jkmunson/RTOS_POD/PLAYER_FIRMWARE/Core/Inc/wav_header.h

unsigned char wav_header_bin[] = {
  0x52, 0x49, 0x46, 0x46, 0x24, 0xf8, 0x2b, 0x03, 0x57, 0x41, 0x56, 0x45,
  0x66, 0x6d, 0x74, 0x20, 0x10, 0x00, 0x00, 0x00, 0x01, 0x00, 0x01, 0x00,
  0x44, 0xac, 0x00, 0x00, 0x10, 0xb1, 0x02, 0x00, 0x04, 0x00, 0x10, 0x00,
  0x64, 0x61, 0x74, 0x61, 0x50, 0x75, 0x0d, 0x00
};
unsigned int wav_header_bin_len = 44;
