jkmunson/RTOS_POD/PLAYER_FIRMWARE/Core/Src/jeremy.c

#include "FreeRTOS.h"
#include "task.h"
#include "cmsis_os.h"
#include "stm32g4xx_hal.h"
#include "stm32g4xx_hal_dac.h"
#include "stm32g4xx_hal_dma.h"
#include "stm32g4xx_hal_tim.h"
#include "main.h"
#include "console.h"
#include "buttons.h"


#include <string.h>
#include <stdio.h>

extern DMA_HandleTypeDef hdma_dac1_ch1;
#define AUD_GREEN_L_DMA hdma_dac1_ch1;

extern UART_HandleTypeDef huart5;
//DAC_DHR12LD

size_t audio_dma_current_index;

void update_green_DMA_addr(void){
	audio_dma_current_index = (audio_dma_current_index+4)%AUD_BUFFER_SIZE;
	const char *tim_msg = "DMA Update started or wrapped\n";
	HAL_UART_Transmit(&huart5,tim_msg,strlen(tim_msg), 0xFFFF);
	if ((audio_dma_current_index==0))	HAL_UART_Transmit(&huart5,tim_msg,strlen(tim_msg), 0xFFFF);
}

size_t get_audio_buffer_current_index(void){
	return audio_dma_current_index;
}


void jeremy_main(void *ignore __attribute__ ((unused))) {
	while(1){
		vTaskDelay(100);
		//console_print_blocked("Hi\n", 200);
	}
	/*
	const char *jeremy_main_msg = "Jeremy: Entered Jeremy Main\n";
	const char *jeremy_main_cb = "Jeremy: Registered timer callback\n";
	const char *jeremy_main_dma = "Jeremy: Initiated DMA\n";
	const char *jeremy_main_tim = "Jeremy: Initiated Timer\n";
	char buf[75];

	HAL_UART_Transmit(&huart5,jeremy_main_msg,strlen(jeremy_main_msg), 0xFFFF);

	HAL_TIM_Base_Start(&AUDIO_44_1_KHZ_TIMER);
	HAL_UART_Transmit(&huart5,jeremy_main_tim,strlen(jeremy_main_tim), 0xFFFF);
	HAL_DAC_Start(&AUD_GREEN_DAC, DAC_CHANNEL_1);
	HAL_DAC_Start(&AUD_GREEN_DAC, DAC_CHANNEL_2);

	HAL_DAC_Start_DMA(&AUD_GREEN_DAC, DAC_CHANNEL_1, (uint32_t*)audio_buffer, (AUD_BUFFER_SIZE>>2)-1 , DAC_ALIGN_12B_L);
	HAL_DAC_Start_DMA(&AUD_GREEN_DAC, DAC_CHANNEL_2, (uint32_t*)(audio_buffer+2), (AUD_BUFFER_SIZE>>2)-1 , DAC_ALIGN_12B_L);



	HAL_UART_Transmit(&huart5,jeremy_main_dma,strlen(jeremy_main_dma), 0xFFFF);
	audio_dma_current_index = 0; //Reset the index now, in case it had counted up before we started DMA. its okay to be a ways behind the dma.
	for(int i=0; 1; i++){
		sprintf(buf, "Jeremy: Uptime: %d\n", i, audio_dma_current_index);
		HAL_UART_Transmit(&huart5, buf, strlen(buf), 0xFFFF);
		vTaskDelay(1000);
	}*/
	vTaskSuspend(NULL); //LEAVE AT THE END
	vTaskDelete(NULL);
}
